reporafin/cascaded-variable-linear-power-supply/Simulation/main_design.asc

C1: cap; 2200µ; V=50 Irms=1.53 Rser=0.037 Lser=0 mfg="Nichicon" pn="UPR1H222MRH" type="Al electrolytic"
C2: cap; .1µ
C4: cap; .33µ
C5: cap; .1µ
C6: cap; 0.33µ; V=50 Irms=813m Rser=0.0897233 Lser=0 mfg="KEMET" pn="C1206C334K5RAC" type="X7R"
C7: cap; .1µ
C8: cap; 10µ
C9: cap; 10µ
D1: diode; 1N4007
D2: diode; 1N4007
D3: diode; 1N4007
D4: diode; 1N4007
D5: diode
D6: diode
R1: res; 240
R2: res; {Rpot}
R3: res; 1k
R4: res; 1k
R5: res; 1k
R6: res; 1k
U1: LT317A
U2: LT1086-12
U3: LT1086-5
U4: LT1086-3.3
V1: voltage; SINE(0 34 60)
Named nets: 0
.tran 100m
.step param Rpot 10 5k 1k
